thenameiscobmarley/pg-1-pedal/PG-Pedal-1/05-Wiring-and-Schematics/seed-socket-board.png

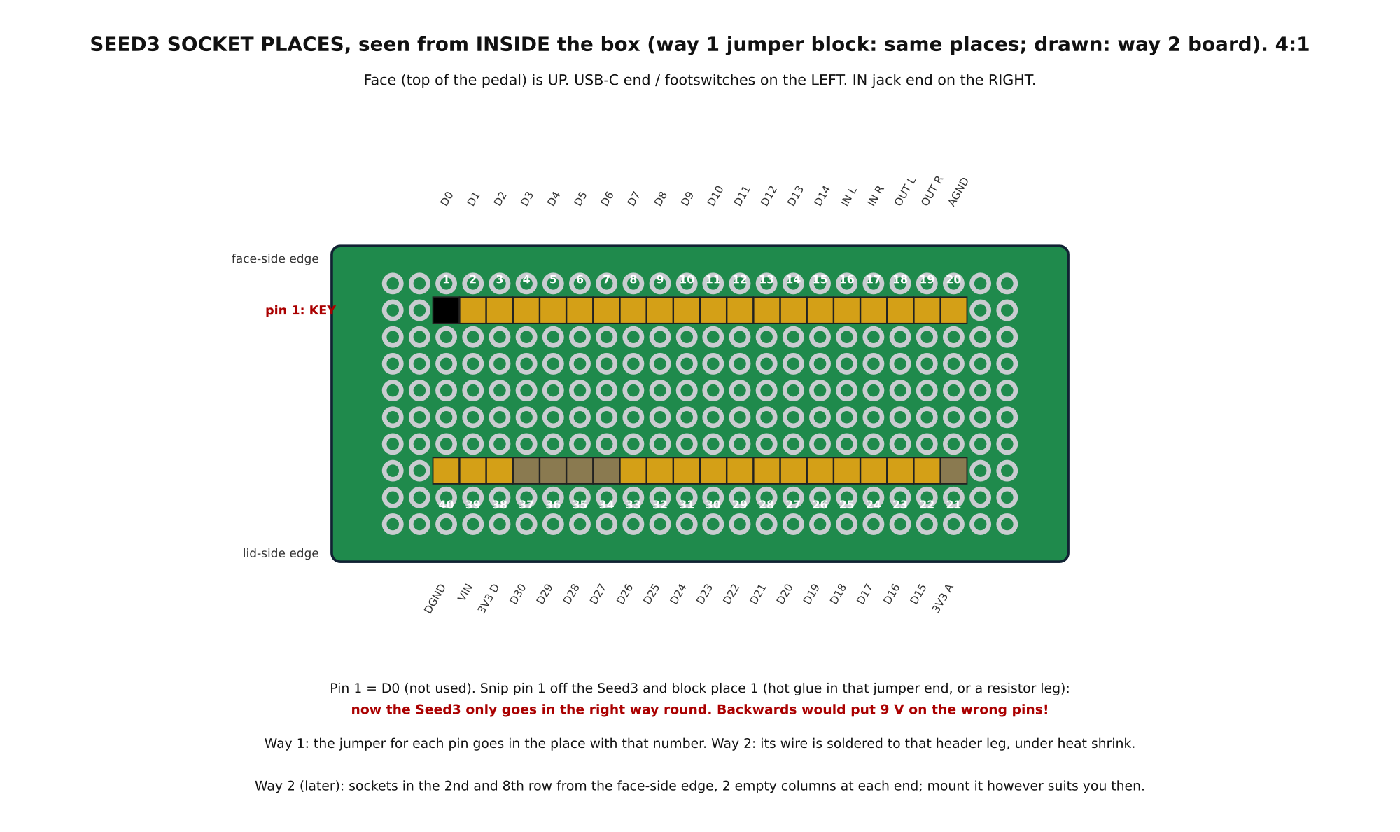
PG-Pedal-1/05-Wiring-and-Schematics/seed-socket-board.png
