thenameiscobmarley/pg-1-pedal/PG-Pedal-1/05-Wiring-and-Schematics/wiring-diagram.png

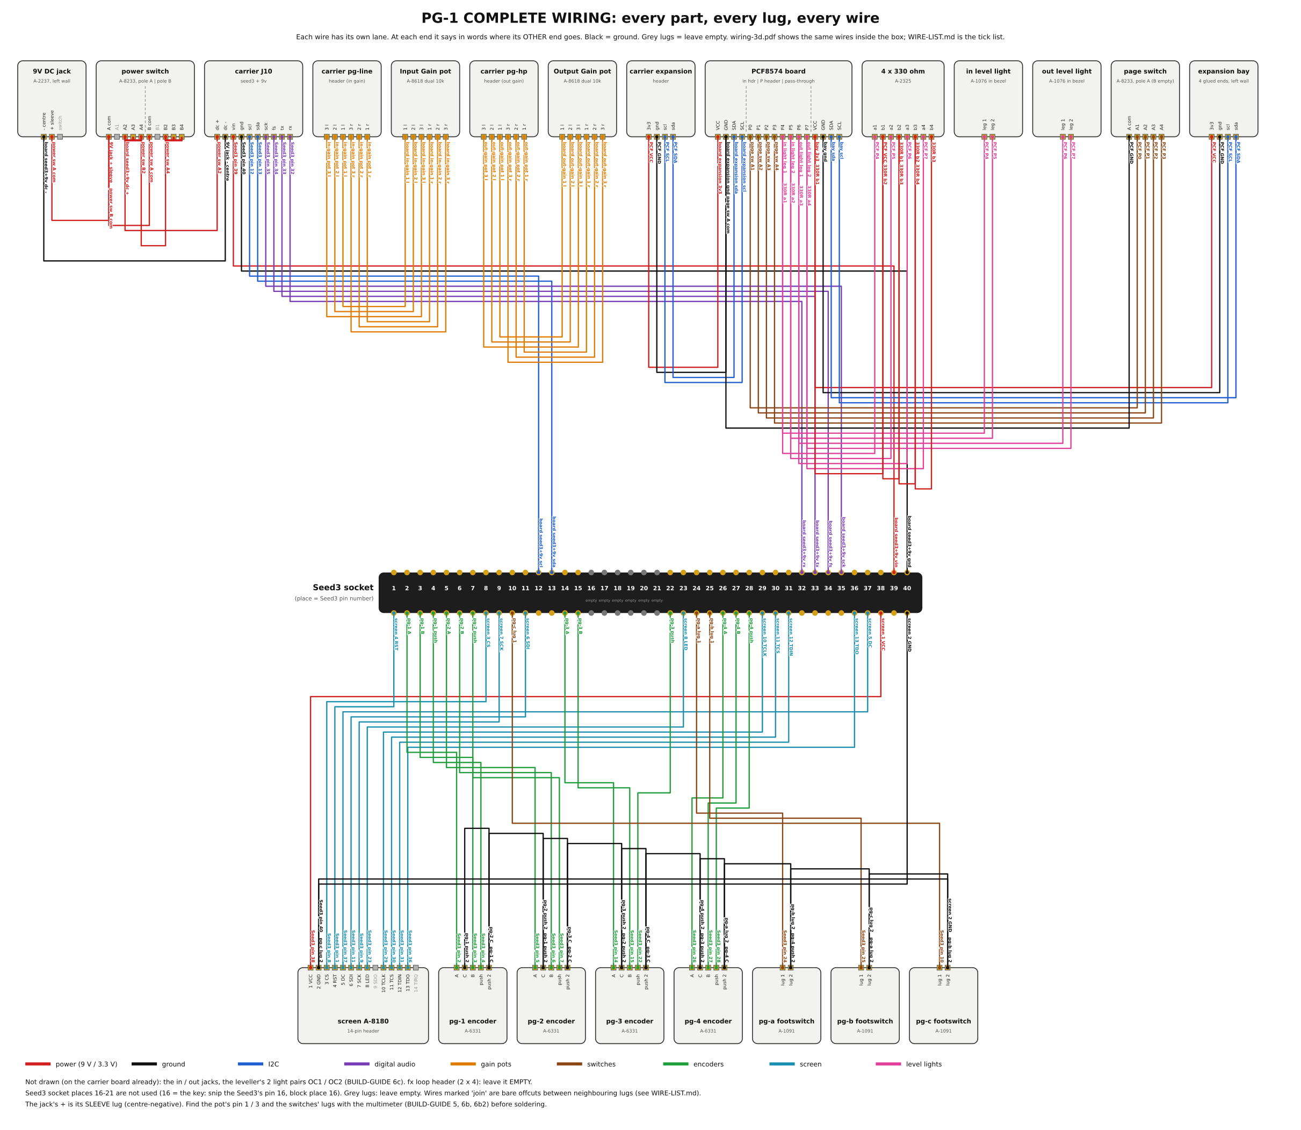
PG-Pedal-1/05-Wiring-and-Schematics/wiring-diagram.png
